Curtis-05/DumbFCC/HTML/images/cat_pdf_drill_map_DumbFCC-NPTH_drill_map.png

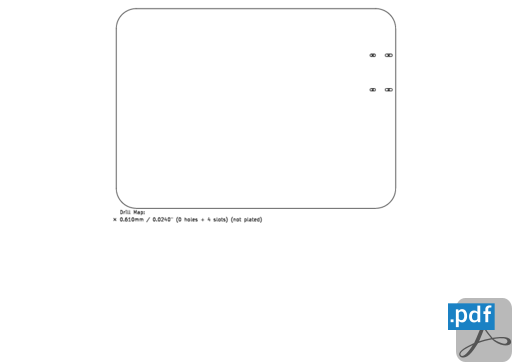
HTML/images/cat_pdf_drill_map_DumbFCC-NPTH_drill_map.png
