Curtis-05/DumbFCC/HTML/images/cat_png_3d_viewer_top_DumbFCC-top.png

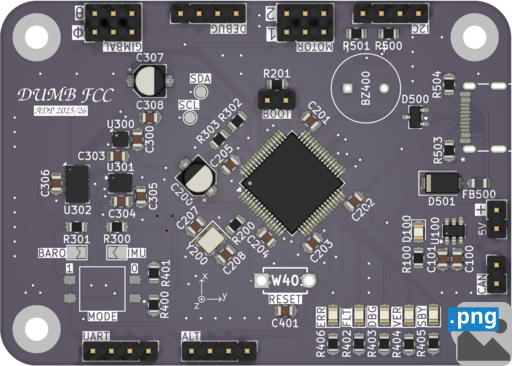
HTML/images/cat_png_3d_viewer_top_DumbFCC-top.png
